CuriousTech/WiFi-Car-Sentry/Arduino/eeMem.cpp

#include "eeMem.h"
#include <EEPROM.h>

eeSet ee = { sizeof(eeSet), 0xAAAA,
  "",      // saved SSID
  "", // router password
  -5,             // TZ
  false,           // OLED
  83,             // hostPort
  192 | (168<<8) | (100<<24), // hostIP 192.168.0.100
  10,             // time_off
  true,           // get_time
  false,           // get_loc
  true,           // roaming
  false,          // loc set mode
  "",            // lat
  "",            // lon
  "host's gloabl IP", // domain (or global IP)
  0, // res
};

eeMem::eeMem()
{
  EEPROM.begin(512);

  uint8_t data[sizeof(eeSet)];
  uint16_t *pwTemp = (uint16_t *)data;

  int addr = 0;
  for(int i = 0; i < sizeof(eeSet); i++, addr++)
  {
    data[i] = EEPROM.read( addr );
  }

  if(pwTemp[0] != sizeof(eeSet)) return; // revert to defaults if struct size changes
  uint16_t sum = pwTemp[1];
  pwTemp[1] = 0;
  pwTemp[1] = Fletcher16(data, sizeof(eeSet) );
  if(pwTemp[1] != sum) return; // revert to defaults if sum fails
  memcpy(&ee, data, sizeof(eeSet) );
}

void eeMem::update() // write the settings if changed
{
  uint16_t old_sum = ee.sum;
  ee.sum = 0;
  ee.sum = Fletcher16((uint8_t*)&ee, sizeof(eeSet));

  if(old_sum == ee.sum)
    return; // Nothing has changed?

  uint16_t addr = 0;
  uint8_t *pData = (uint8_t *)&ee;
  for(int i = 0; i < sizeof(eeSet); i++, addr++)
  {
    EEPROM.write(addr, pData[i] );
  }
  EEPROM.commit();
}

uint16_t eeMem::Fletcher16( uint8_t* data, int count)
{
   uint16_t sum1 = 0;
   uint16_t sum2 = 0;

   for( int index = 0; index < count; ++index )
   {
      sum1 = (sum1 + data[index]) % 255;
      sum2 = (sum2 + sum1) % 255;
   }

   return (sum2 << 8) | sum1;
}
